esynr3z/vfd-ps/misc/lm2576-negative/lm2576-negative.asc

C1: cap; 220µF
C2: cap; 100µ
D1: zener; 1N5378B
L1: ind; 68µH
R1: res; 18.67k
R2: res; 1k
Rload: res; 100
U1: LM2576_TRANS
V1: voltage; 5; Rser=0.1
Named nets: 0, VEE, VCC, FB, OUT
.tran 0 30m 1u 1u uic
