esynr3z/vfd-ps/misc/lm4871-filament/lm4871-filament.asc

C1: cap; 1µF
C2: cap; 10µ
C3: cap; 10µ
D1: zener; 1N750
R6: res; 100
R7: res; 100
Rf: res; 58
Rtrim1: res; 10
Rtrim2: res; 10
U1: LM4871
V1: voltage; 5; Rser=0.1
V2: voltage; -30; Rser=0.1
V3: voltage; PULSE(0 5 0 1n 1n 20u 40u)
Named nets: 0, Vcc, Vee, F1, F2
.tran 0 100m 10u 10u uic
Self oscillation scheme (LM9022 datasheet) doesnt working here,
so pulse generator used
