esynr3z/vfd-ps/misc/ad8534-filament/ad8534-filament.asc

C1: cap; 1n
C2: cap; 1µ
C3: cap; 1µ
D1: zener; 1N750
R1: res; 4.7k
R2: res; 10k
R3: res; 10k
R4: res; 10k
R5: res; 10k
R6: res; 100
R7: res; 100
Rf: res; 58
U1: opamp2; ad8534
U2: opamp2; ad8534
V1: voltage; 6; Rser=0.1
V2: voltage; -30; Rser=0.1
Named nets: 0, Vcc, Vee, F1, F2
.inc ad8534.lib
.tran 0 1m 0 10u uic
